CedricBerteletti/rockets-with-arduino/modeles-3d/900_axe_5_mm.FCStd

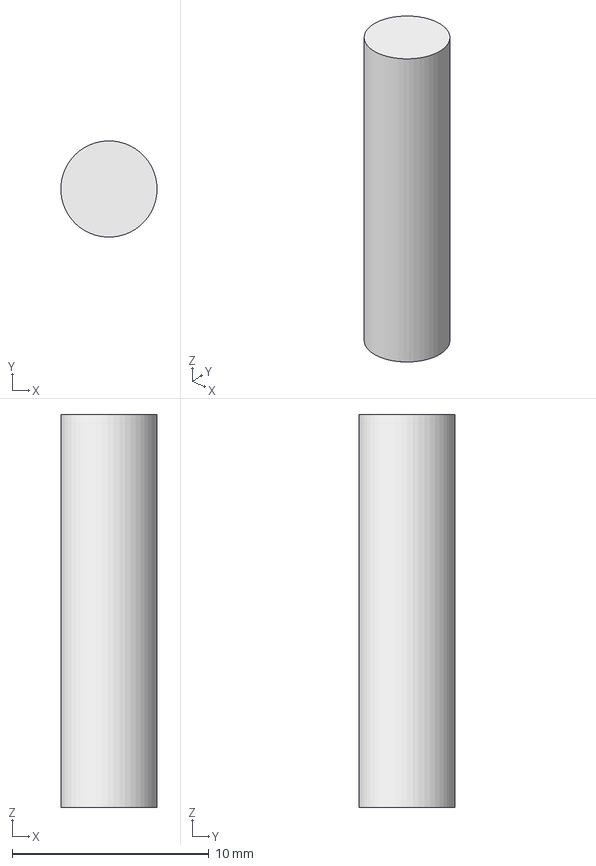
[picture p20: CAD file, 2024-01-03]
modeles-3d/900_axe_5_mm.FCStd
4.90 x 4.90 x 20.0 mm
