CedricBerteletti/rockets-with-arduino/modeles-3d/302_capsule_aileron.FCStd

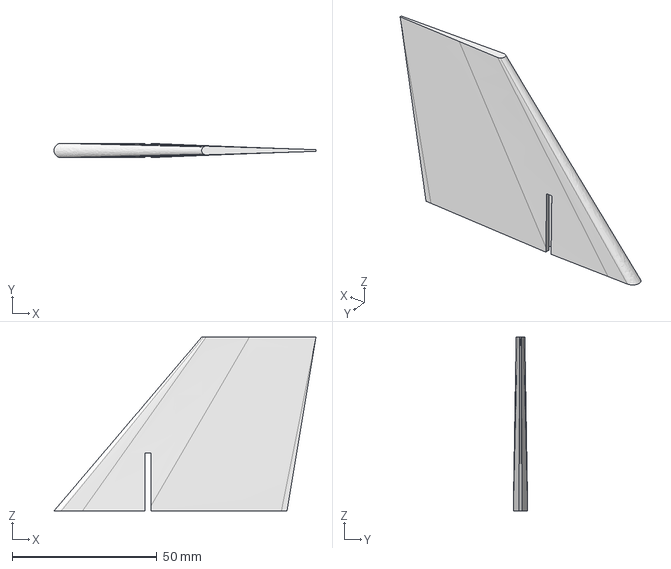
[picture p21: CAD file, 2024-01-03]
modeles-3d/302_capsule_aileron.FCStd
90.5 x 5.00 x 60.0 mm
