CedricBerteletti/rockets-with-arduino/modeles-3d/901_servo_engrenage.FCStd

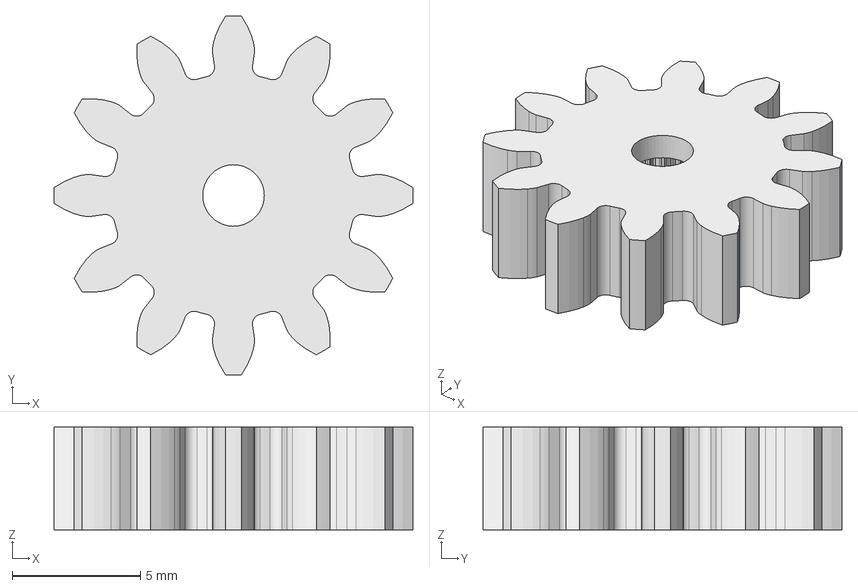
[picture p22: CAD file, 2023-12-29]
modeles-3d/901_servo_engrenage.FCStd
14.0 x 14.0 x 4.00 mm
