CedricBerteletti/rockets-with-arduino/compte-a-rebours/modeles-3d/ensemble.scad

use <boitier.scad>
use <couvercle.scad>

include <constantes.scad>

boitier();

translate ([0, 0, hauteur + epaisseur]) couvercle();
