CedricBerteletti/rockets-with-arduino/logiciel-vol/arduino-nano-33-iot/logiciel-vol/Servomoteur.hpp

/*
 * --------------------------------------------------------------------------
 * Gestion d'un servomoteur
 * --------------------------------------------------------------------------
 * @author Cédric Berteletti
 */

#ifndef Servomoteur_h
#define Servomoteur_h

#include <Arduino.h>
#include <Servo.h>
#include "constants.h"
#include "Logger.hpp"

inline constexpr int SERVO_DECALAGE_PAR_DEFAUT = 90;
inline constexpr float SERVO_PENTE_PAR_DEFAUT = 0.9f;
inline constexpr float SERVO_POSITION_MIN = -100;
inline constexpr float SERVO_POSITION_MAX = 100;

class Servomoteur
{
  public:
    Servomoteur(Logger &logger);
    void init(int id, int broche);
    void setDecalage(int decalage);
    void setPente(float pente);
    void angle(int angle);
    void position(int position);
    void logStatut();
  
  private:
    static const char MODULE_SERVO[];
    char strTmp[LONGUEUR_MAX_CHAINE_CARACTERES];
    Logger &logger;
    Servo servo;
    int id;
    int broche;
    int decalage = SERVO_DECALAGE_PAR_DEFAUT;
    float pente = SERVO_PENTE_PAR_DEFAUT;    
};

#endif
