CedricBerteletti/rockets-with-arduino/logiciel-vol/arduino-nano-33-iot/logiciel-vol/secrets.h

/*
 * --------------------------------------------------------------------------
 * A ne pas commiter une fois renseigné
 * --------------------------------------------------------------------------
 * @author Cédric Berteletti
 */

#ifndef secrets_h
#define secrets_h

// Wifi
inline constexpr char WIFI1_SSID[] = "";
inline constexpr char WIFI1_PASS[] = "";
inline constexpr char WIFI2_SSID[] = "";
inline constexpr char WIFI2_PASS[] = "";

// Code de lancement
inline constexpr char SECRET_COMMAND_CODE[] = "";

#endif
